RELEASE255/ML01_project/05_images/product/ml01-product-02.png

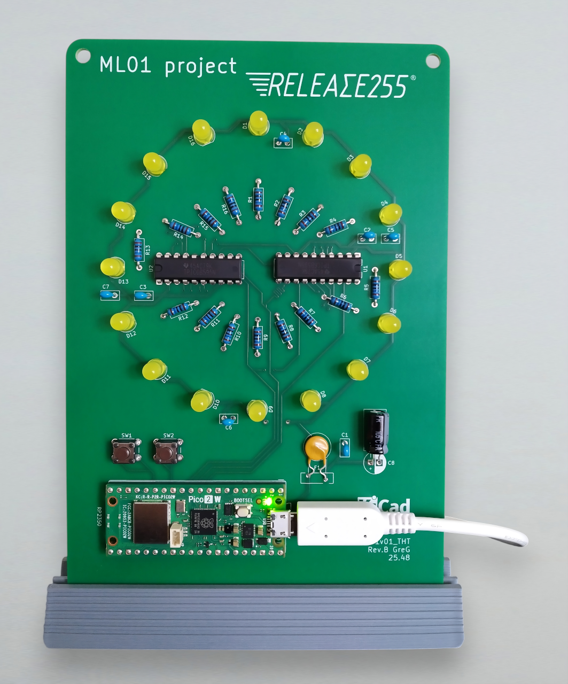
05_images/product/ml01-product-02.png
